ivicak99/universal-esp32-bridge/capinject.kicad_sch

## KiCad design capinject.kicad_sch (2026-05-29)

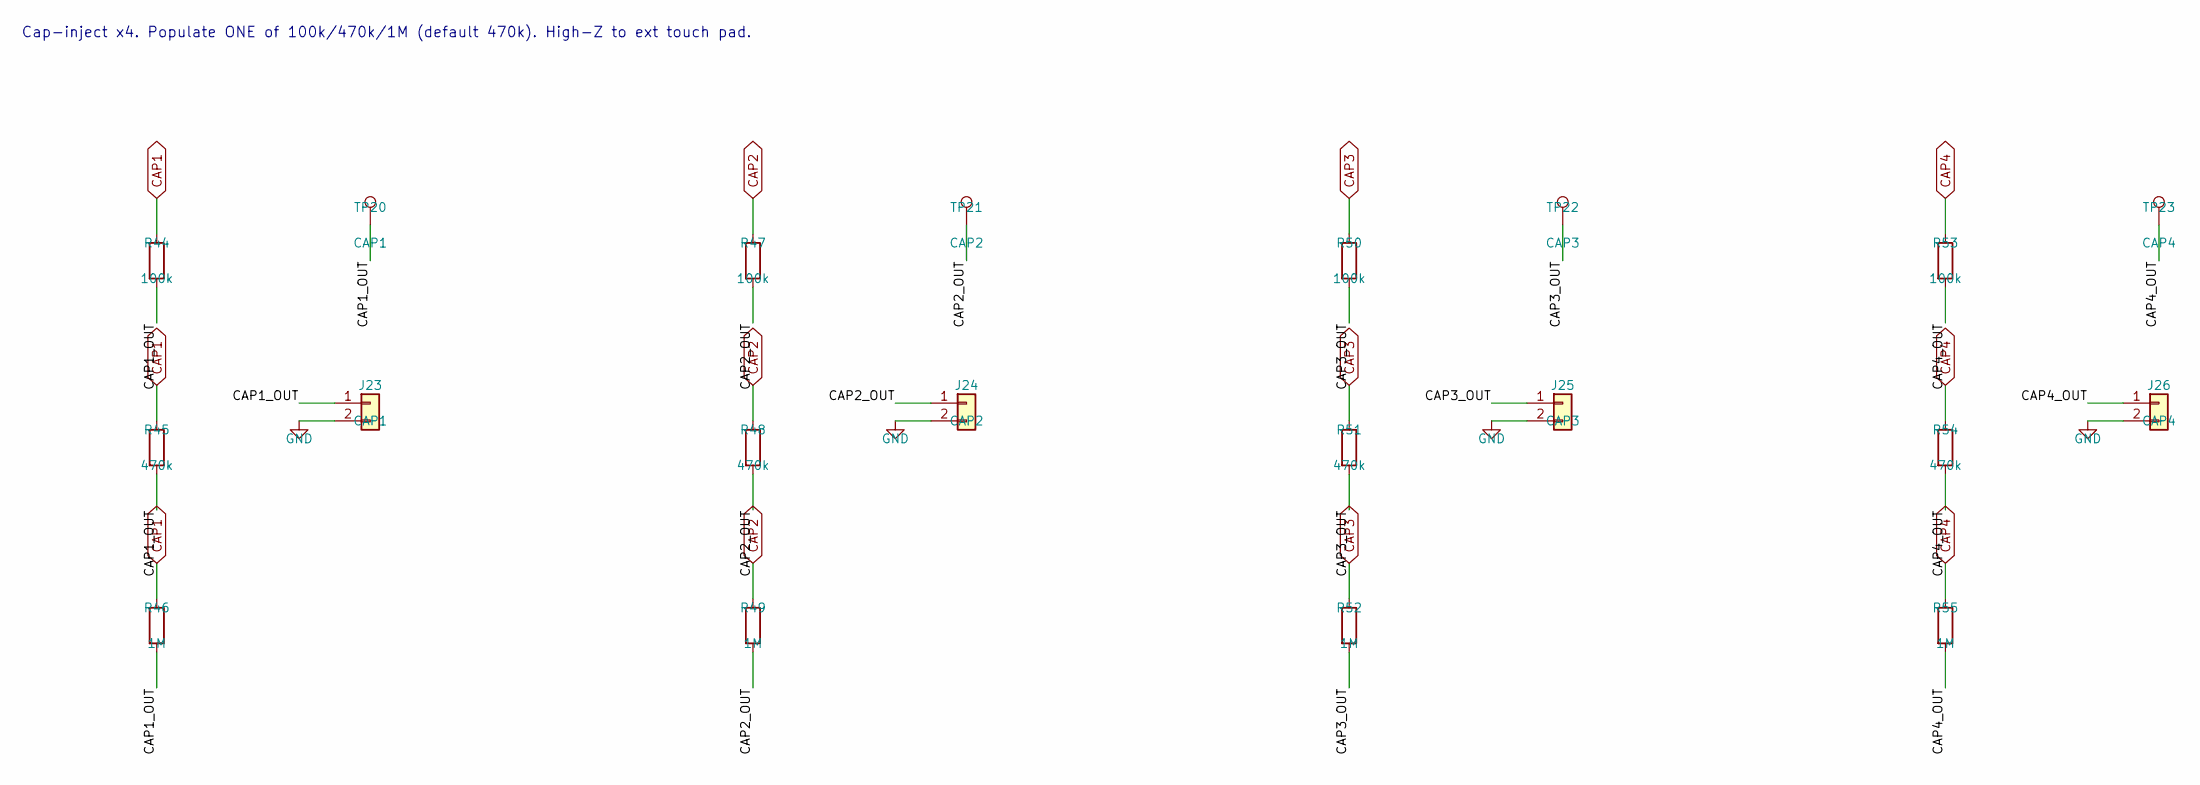
[picture p8: schematic capinject.kicad_sch]

Parts:
J23: CAP1; TerminalBlock_MaiXu_MX126-5.0-02P_1x02_P5.00mm
J24: CAP2; TerminalBlock_MaiXu_MX126-5.0-02P_1x02_P5.00mm
J25: CAP3; TerminalBlock_MaiXu_MX126-5.0-02P_1x02_P5.00mm
J26: CAP4; TerminalBlock_MaiXu_MX126-5.0-02P_1x02_P5.00mm
R44, R47, R50, R53: 100k; R_0603_1608Metric
R45, R48, R51, R54: 470k; R_0603_1608Metric
R46, R49, R52, R55: 1M; R_0603_1608Metric
TP20: CAP1; TestPoint_Pad_D1.5mm
TP21: CAP2; TestPoint_Pad_D1.5mm
TP22: CAP3; TestPoint_Pad_D1.5mm
TP23: CAP4; TestPoint_Pad_D1.5mm

Connections:
CAP1: R44.1, R45.1, R46.1
CAP1_OUT: J23.1, R44.2, R45.2, R46.2, TP20.1
CAP2: R47.1, R48.1, R49.1
CAP2_OUT: J24.1, R47.2, R48.2, R49.2, TP21.1
CAP3: R50.1, R51.1, R52.1
CAP3_OUT: J25.1, R50.2, R51.2, R52.2, TP22.1
CAP4: R53.1, R54.1, R55.1
CAP4_OUT: J26.1, R53.2, R54.2, R55.2, TP23.1
GND: J23.2, J24.2, J25.2, J26.2

Notes on the sheet:
Cap-inject x4. Populate ONE of 100k/470k/1M (default 470k). High-Z to ext touch pad.
