ivicak99/universal-esp32-bridge/inputs.kicad_sch

## KiCad design inputs.kicad_sch (2026-05-29)

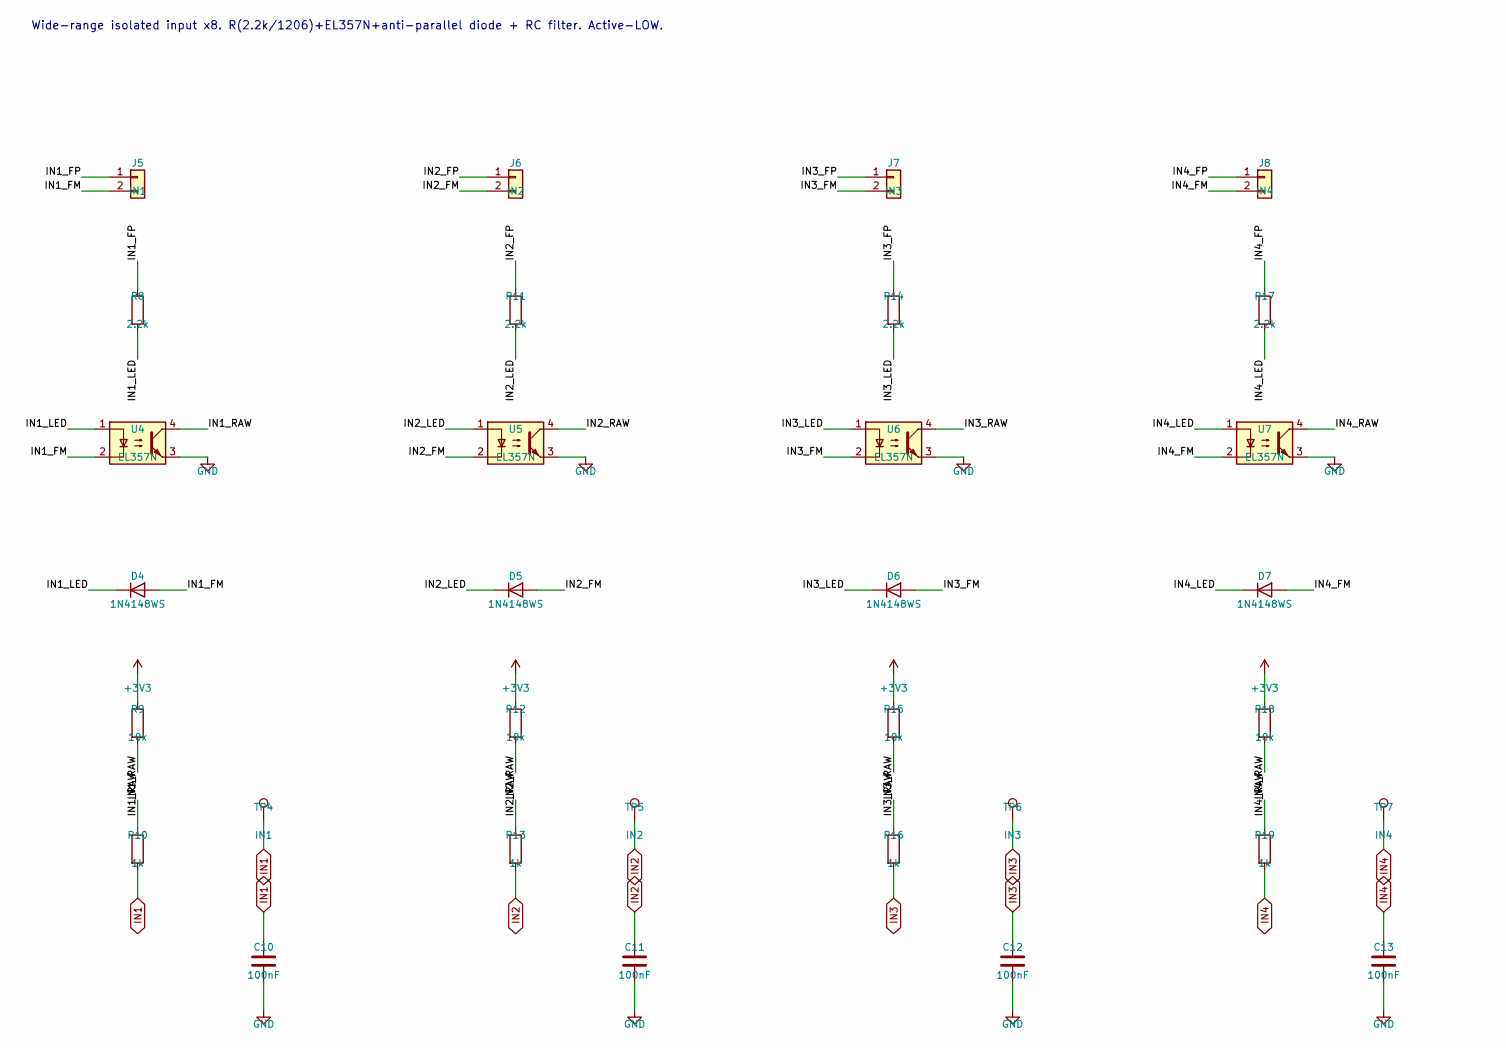
[picture p9: schematic inputs.kicad_sch, part in row 1, column 1]

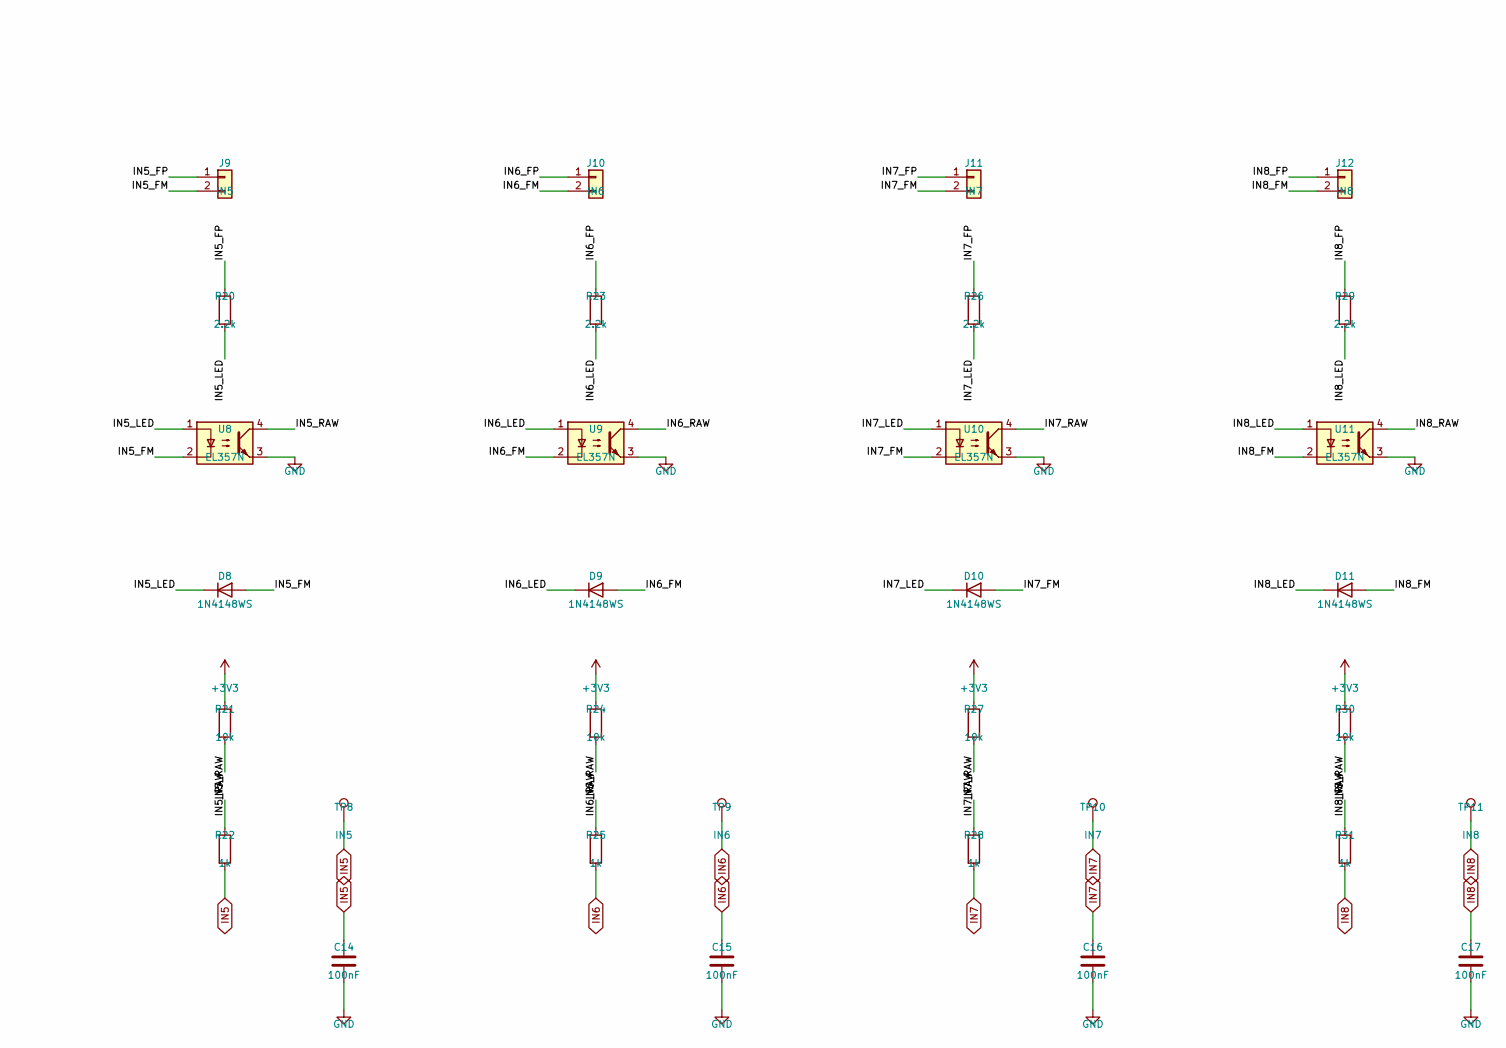
[picture p10: schematic inputs.kicad_sch, part in row 1, column 2]

Parts:
C10, C11, C12, C13, C14, C15, C16, C17: 100nF; C_0603_1608Metric
D4, D5, D6, D7, D8, D9, D10, D11: 1N4148WS; D_SOD-323
J5: IN1; TerminalBlock_MaiXu_MX126-5.0-02P_1x02_P5.00mm
J6: IN2; TerminalBlock_MaiXu_MX126-5.0-02P_1x02_P5.00mm
J7: IN3; TerminalBlock_MaiXu_MX126-5.0-02P_1x02_P5.00mm
J8: IN4; TerminalBlock_MaiXu_MX126-5.0-02P_1x02_P5.00mm
J9: IN5; TerminalBlock_MaiXu_MX126-5.0-02P_1x02_P5.00mm
J10: IN6; TerminalBlock_MaiXu_MX126-5.0-02P_1x02_P5.00mm
J11: IN7; TerminalBlock_MaiXu_MX126-5.0-02P_1x02_P5.00mm
J12: IN8; TerminalBlock_MaiXu_MX126-5.0-02P_1x02_P5.00mm
R8, R11, R14, R17, R20, R23, R26, R29: 2.2k; R_1206_3216Metric
R9, R12, R15, R18, R21, R24, R27, R30: 10k; R_0603_1608Metric
R10, R13, R16, R19, R22, R25, R28, R31: 1k; R_0603_1608Metric
TP4: IN1; TestPoint_Pad_D1.5mm
TP5: IN2; TestPoint_Pad_D1.5mm
TP6: IN3; TestPoint_Pad_D1.5mm
TP7: IN4; TestPoint_Pad_D1.5mm
TP8: IN5; TestPoint_Pad_D1.5mm
TP9: IN6; TestPoint_Pad_D1.5mm
TP10: IN7; TestPoint_Pad_D1.5mm
TP11: IN8; TestPoint_Pad_D1.5mm
U4, U5, U6, U7, U8, U9, U10, U11: EL357N; EL357N_SOP-4

Connections:
+3V3: R9.1, R12.1, R15.1, R18.1, R21.1, R24.1, R27.1, R30.1
GND: C10.2, C11.2, C12.2, C13.2, C14.2, C15.2, C16.2, C17.2, U4.3, U5.3, U6.3, U7.3, U8.3, U9.3, U10.3, U11.3
IN1: C10.1, R10.2, TP4.1
IN1_FM: D4.2 (A), J5.2, U4.2
IN1_FP: J5.1, R8.1
IN1_LED: D4.1 (K), R8.2, U4.1
IN1_RAW: R9.2, R10.1, U4.4
IN2: C11.1, R13.2, TP5.1
IN2_FM: D5.2 (A), J6.2, U5.2
IN2_FP: J6.1, R11.1
IN2_LED: D5.1 (K), R11.2, U5.1
IN2_RAW: R12.2, R13.1, U5.4
IN3: C12.1, R16.2, TP6.1
IN3_FM: D6.2 (A), J7.2, U6.2
IN3_FP: J7.1, R14.1
IN3_LED: D6.1 (K), R14.2, U6.1
IN3_RAW: R15.2, R16.1, U6.4
IN4: C13.1, R19.2, TP7.1
IN4_FM: D7.2 (A), J8.2, U7.2
IN4_FP: J8.1, R17.1
IN4_LED: D7.1 (K), R17.2, U7.1
IN4_RAW: R18.2, R19.1, U7.4
IN5: C14.1, R22.2, TP8.1
IN5_FM: D8.2 (A), J9.2, U8.2
IN5_FP: J9.1, R20.1
IN5_LED: D8.1 (K), R20.2, U8.1
IN5_RAW: R21.2, R22.1, U8.4
IN6: C15.1, R25.2, TP9.1
IN6_FM: D9.2 (A), J10.2, U9.2
IN6_FP: J10.1, R23.1
IN6_LED: D9.1 (K), R23.2, U9.1
IN6_RAW: R24.2, R25.1, U9.4
IN7: C16.1, R28.2, TP10.1
IN7_FM: D10.2 (A), J11.2, U10.2
IN7_FP: J11.1, R26.1
IN7_LED: D10.1 (K), R26.2, U10.1
IN7_RAW: R27.2, R28.1, U10.4
IN8: C17.1, R31.2, TP11.1
IN8_FM: D11.2 (A), J12.2, U11.2
IN8_FP: J12.1, R29.1
IN8_LED: D11.1 (K), R29.2, U11.1
IN8_RAW: R30.2, R31.1, U11.4

Notes on the sheet:
Wide-range isolated input x8. R(2.2k/1206)+EL357N+anti-parallel diode + RC filter. Active-LOW.
