ivicak99/universal-esp32-bridge/mcu.kicad_sch

## KiCad design mcu.kicad_sch (2026-05-29)

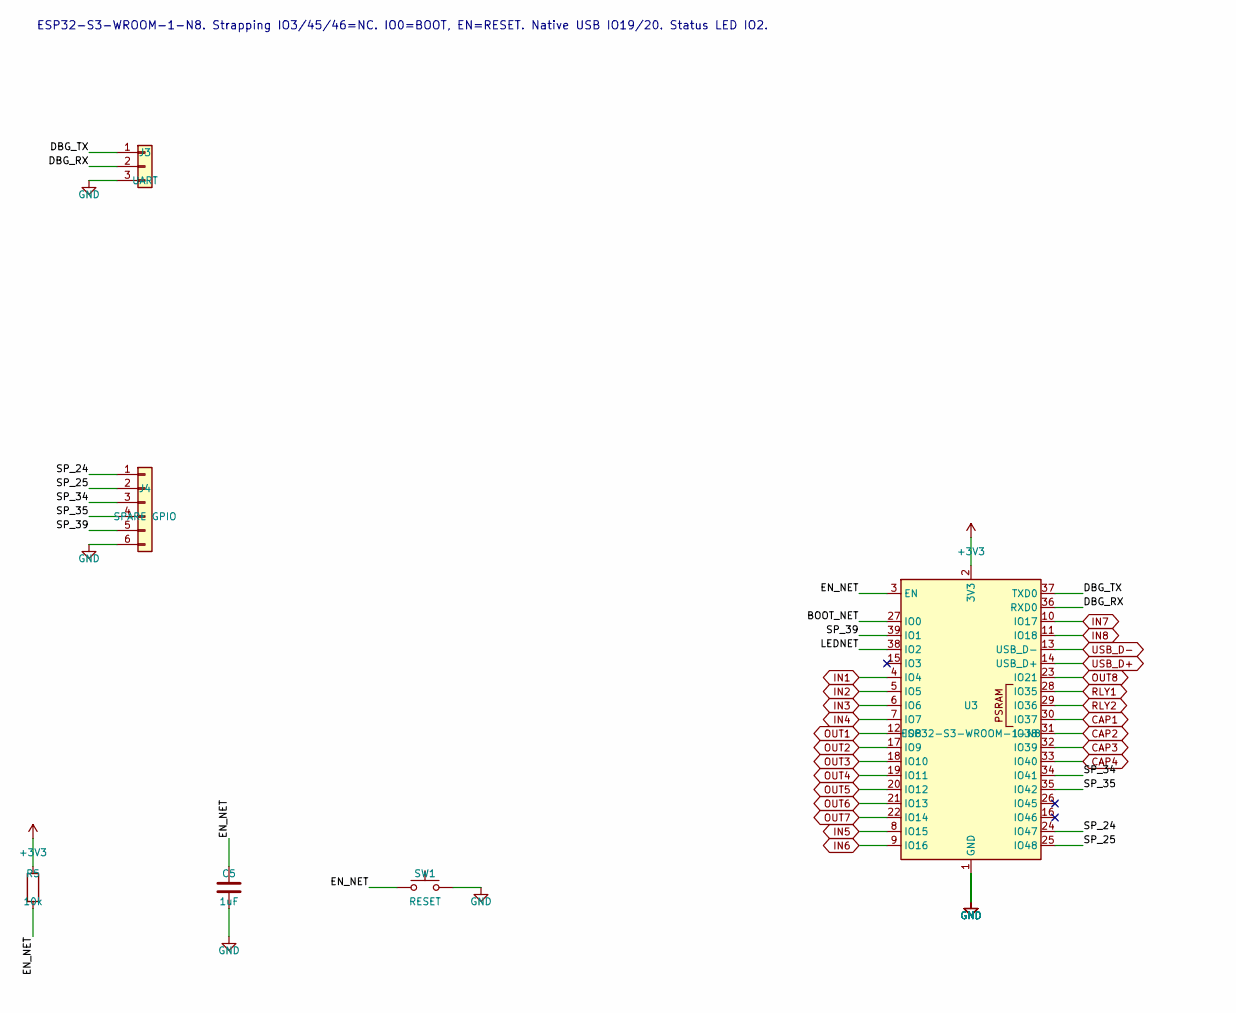
[picture p11: schematic mcu.kicad_sch, part in row 1, column 1]

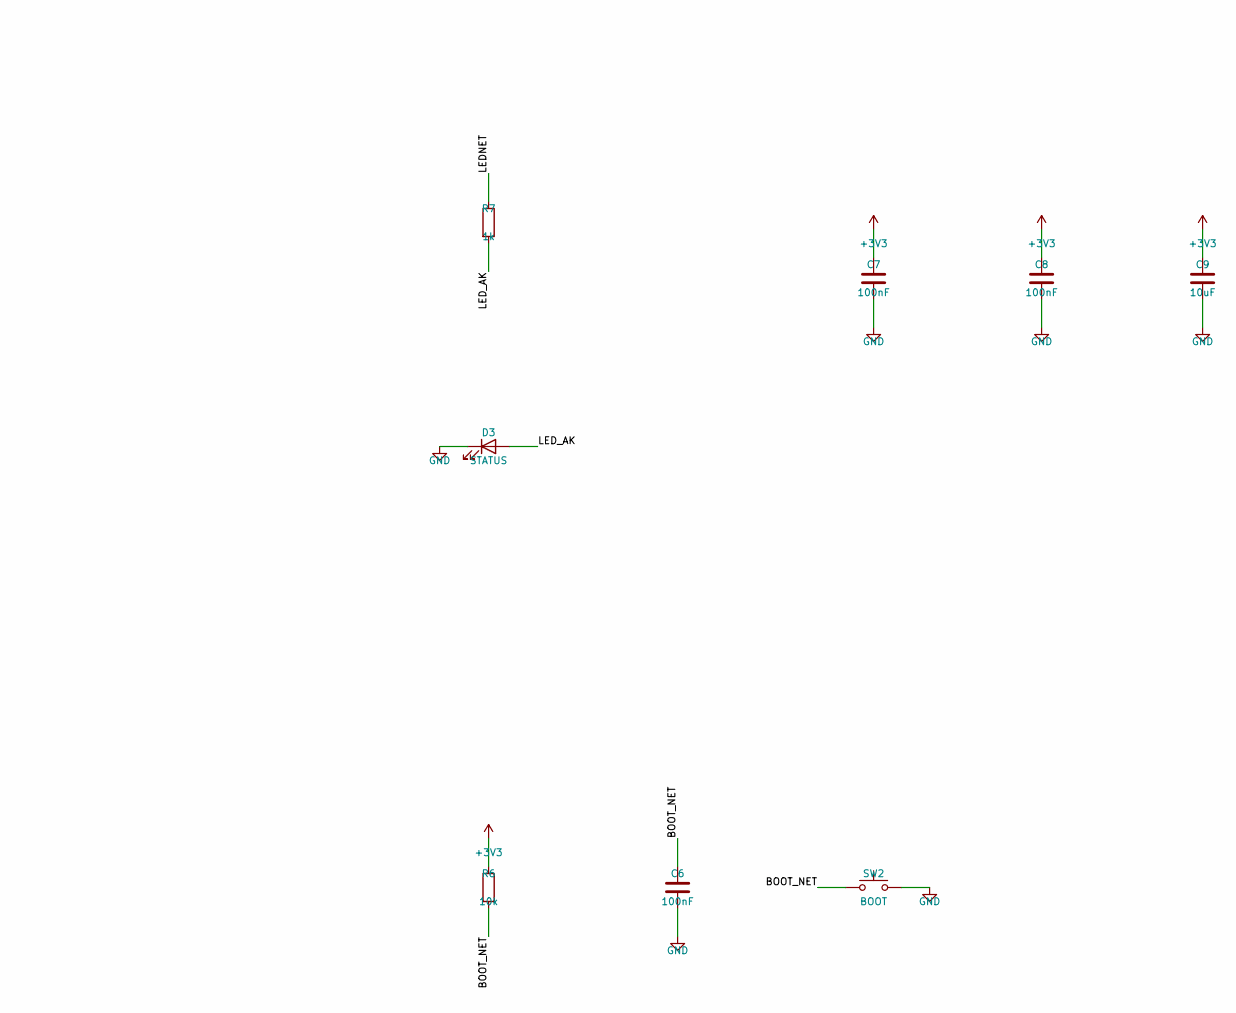
[picture p12: schematic mcu.kicad_sch, part in row 1, column 2]

Parts:
C5: 1uF; C_0603_1608Metric
C6, C7, C8: 100nF; C_0603_1608Metric
C9: 10uF; C_0603_1608Metric
D3: STATUS; LED_0603_1608Metric
J3: UART; PinHeader_1x03_P2.54mm_Vertical
J4: SPARE GPIO; PinHeader_1x06_P2.54mm_Vertical
R5, R6: 10k; R_0603_1608Metric
R7: 1k; R_0603_1608Metric
SW1: RESET; Panasonic_EVQPUJ_EVQPUA
SW2: BOOT; Panasonic_EVQPUJ_EVQPUA
U3: ESP32-S3-WROOM-1-N8; ESP32-S3-WROOM-1

Connections:
+3V3: C7.1, C8.1, C9.1, R5.1, R6.1, U3.2 (3V3)
BOOT_NET: C6.1, R6.2, SW2.1, U3.27 (IO0)
CAP1: U3.30 (IO37)
CAP2: U3.31 (IO38)
CAP3: U3.32 (IO39)
CAP4: U3.33 (IO40)
DBG_RX: J3.2, U3.36 (RXD0)
DBG_TX: J3.1, U3.37 (TXD0)
EN_NET: C5.1, R5.2, SW1.1, U3.3 (EN)
GND: C5.2, C6.2, C7.2, C8.2, C9.2, D3.1 (K), J3.3, J4.6, SW1.2, SW2.2, U3.1 (GND), U3.40 (GND), U3.41 (GND)
IN1: U3.4 (IO4)
IN2: U3.5 (IO5)
IN3: U3.6 (IO6)
IN4: U3.7 (IO7)
IN5: U3.8 (IO15)
IN6: U3.9 (IO16)
IN7: U3.10 (IO17)
IN8: U3.11 (IO18)
LEDNET: R7.1, U3.38 (IO2)
LED_AK: D3.2 (A), R7.2
OUT1: U3.12 (IO8)
OUT2: U3.17 (IO9)
OUT3: U3.18 (IO10)
OUT4: U3.19 (IO11)
OUT5: U3.20 (IO12)
OUT6: U3.21 (IO13)
OUT7: U3.22 (IO14)
OUT8: U3.23 (IO21)
RLY1: U3.28 (IO35)
RLY2: U3.29 (IO36)
SP_24: J4.1, U3.24 (IO47)
SP_25: J4.2, U3.25 (IO48)
SP_34: J4.3, U3.34 (IO41)
SP_35: J4.4, U3.35 (IO42)
SP_39: J4.5, U3.39 (IO1)
USB_D+: U3.14 (USB_D+)
USB_D-: U3.13 (USB_D-)

Notes on the sheet:
ESP32-S3-WROOM-1-N8. Strapping IO3/45/46=NC. IO0=BOOT, EN=RESET. Native USB IO19/20. Status LED IO2.
