ivicak99/universal-esp32-bridge/photomos.kicad_sch

## KiCad design photomos.kicad_sch (2026-05-29)

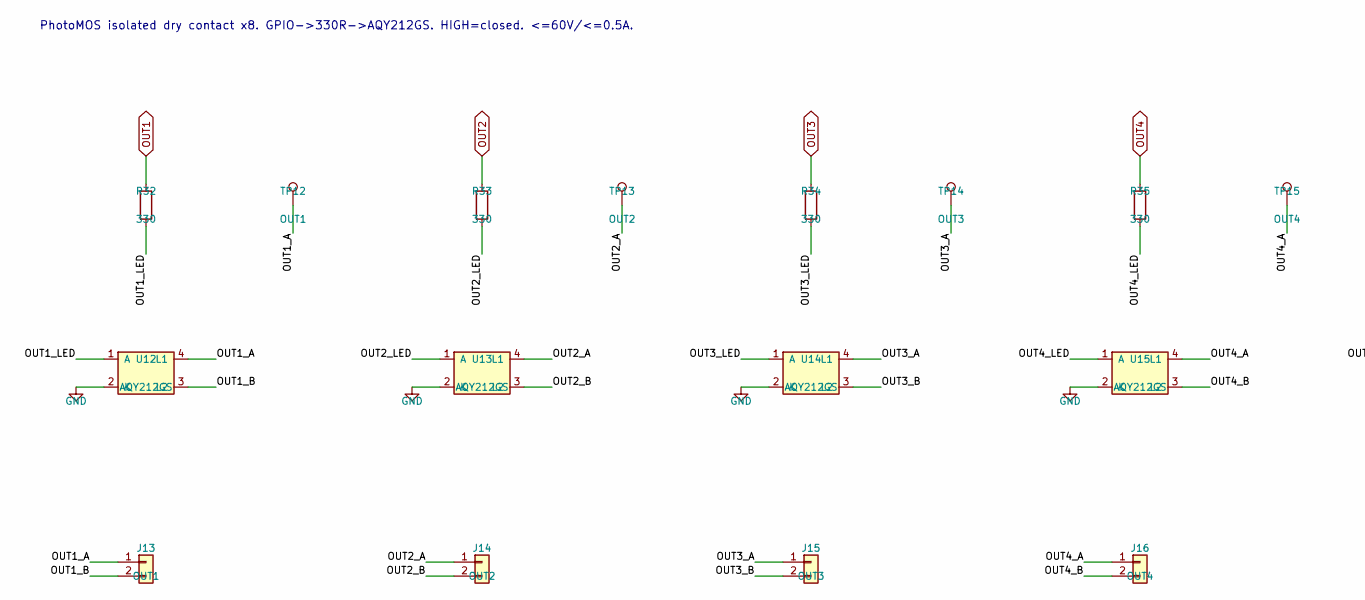
[picture p13: schematic photomos.kicad_sch, part in row 1, column 1]

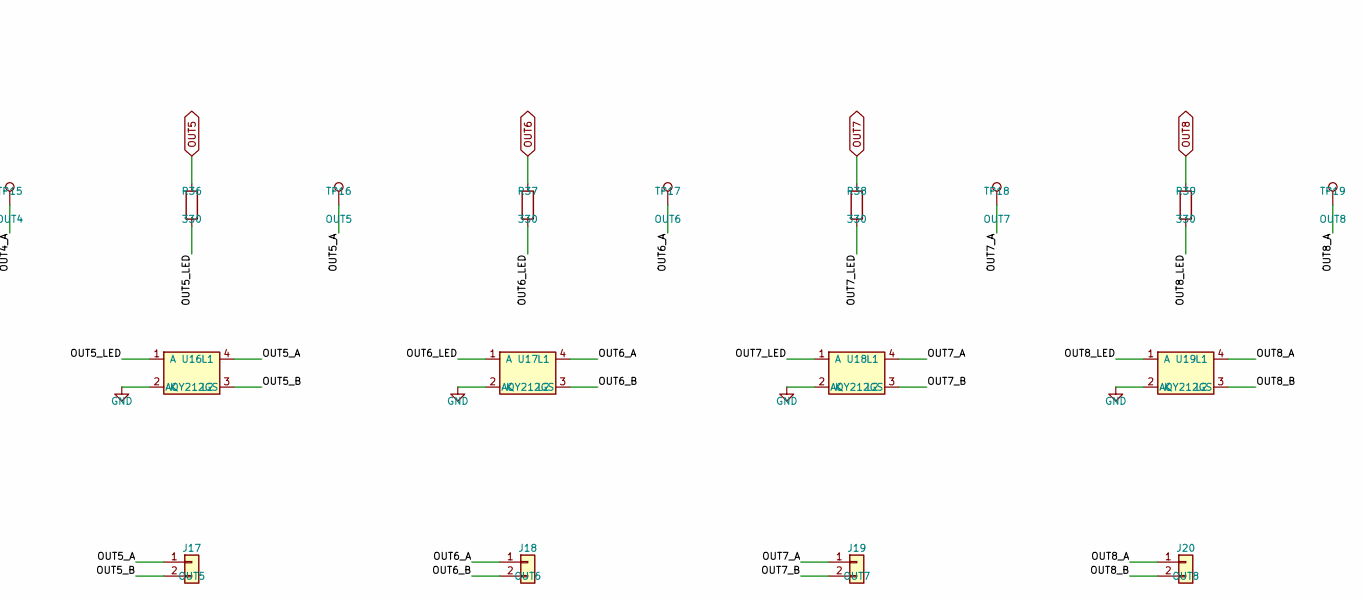
[picture p14: schematic photomos.kicad_sch, part in row 1, column 2]

Parts:
J13: OUT1; TerminalBlock_MaiXu_MX126-5.0-02P_1x02_P5.00mm
J14: OUT2; TerminalBlock_MaiXu_MX126-5.0-02P_1x02_P5.00mm
J15: OUT3; TerminalBlock_MaiXu_MX126-5.0-02P_1x02_P5.00mm
J16: OUT4; TerminalBlock_MaiXu_MX126-5.0-02P_1x02_P5.00mm
J17: OUT5; TerminalBlock_MaiXu_MX126-5.0-02P_1x02_P5.00mm
J18: OUT6; TerminalBlock_MaiXu_MX126-5.0-02P_1x02_P5.00mm
J19: OUT7; TerminalBlock_MaiXu_MX126-5.0-02P_1x02_P5.00mm
J20: OUT8; TerminalBlock_MaiXu_MX126-5.0-02P_1x02_P5.00mm
R32, R33, R34, R35, R36, R37, R38, R39: 330; R_0603_1608Metric
TP12: OUT1; TestPoint_Pad_D1.5mm
TP13: OUT2; TestPoint_Pad_D1.5mm
TP14: OUT3; TestPoint_Pad_D1.5mm
TP15: OUT4; TestPoint_Pad_D1.5mm
TP16: OUT5; TestPoint_Pad_D1.5mm
TP17: OUT6; TestPoint_Pad_D1.5mm
TP18: OUT7; TestPoint_Pad_D1.5mm
TP19: OUT8; TestPoint_Pad_D1.5mm
U12, U13, U14, U15, U16, U17, U18, U19: AQY212GS; AQY212GS_SOP-4

Connections:
GND: U12.2 (K), U13.2 (K), U14.2 (K), U15.2 (K), U16.2 (K), U17.2 (K), U18.2 (K), U19.2 (K)
OUT1: R32.1
OUT1_A: J13.1, TP12.1, U12.4 (L1)
OUT1_B: J13.2, U12.3 (L2)
OUT1_LED: R32.2, U12.1 (A)
OUT2: R33.1
OUT2_A: J14.1, TP13.1, U13.4 (L1)
OUT2_B: J14.2, U13.3 (L2)
OUT2_LED: R33.2, U13.1 (A)
OUT3: R34.1
OUT3_A: J15.1, TP14.1, U14.4 (L1)
OUT3_B: J15.2, U14.3 (L2)
OUT3_LED: R34.2, U14.1 (A)
OUT4: R35.1
OUT4_A: J16.1, TP15.1, U15.4 (L1)
OUT4_B: J16.2, U15.3 (L2)
OUT4_LED: R35.2, U15.1 (A)
OUT5: R36.1
OUT5_A: J17.1, TP16.1, U16.4 (L1)
OUT5_B: J17.2, U16.3 (L2)
OUT5_LED: R36.2, U16.1 (A)
OUT6: R37.1
OUT6_A: J18.1, TP17.1, U17.4 (L1)
OUT6_B: J18.2, U17.3 (L2)
OUT6_LED: R37.2, U17.1 (A)
OUT7: R38.1
OUT7_A: J19.1, TP18.1, U18.4 (L1)
OUT7_B: J19.2, U18.3 (L2)
OUT7_LED: R38.2, U18.1 (A)
OUT8: R39.1
OUT8_A: J20.1, TP19.1, U19.4 (L1)
OUT8_B: J20.2, U19.3 (L2)
OUT8_LED: R39.2, U19.1 (A)

Notes on the sheet:
PhotoMOS isolated dry contact x8. GPIO->330R->AQY212GS. HIGH=closed. <=60V/<=0.5A.
