ivicak99/universal-esp32-bridge/power.kicad_sch

## KiCad design power.kicad_sch (2026-05-29)

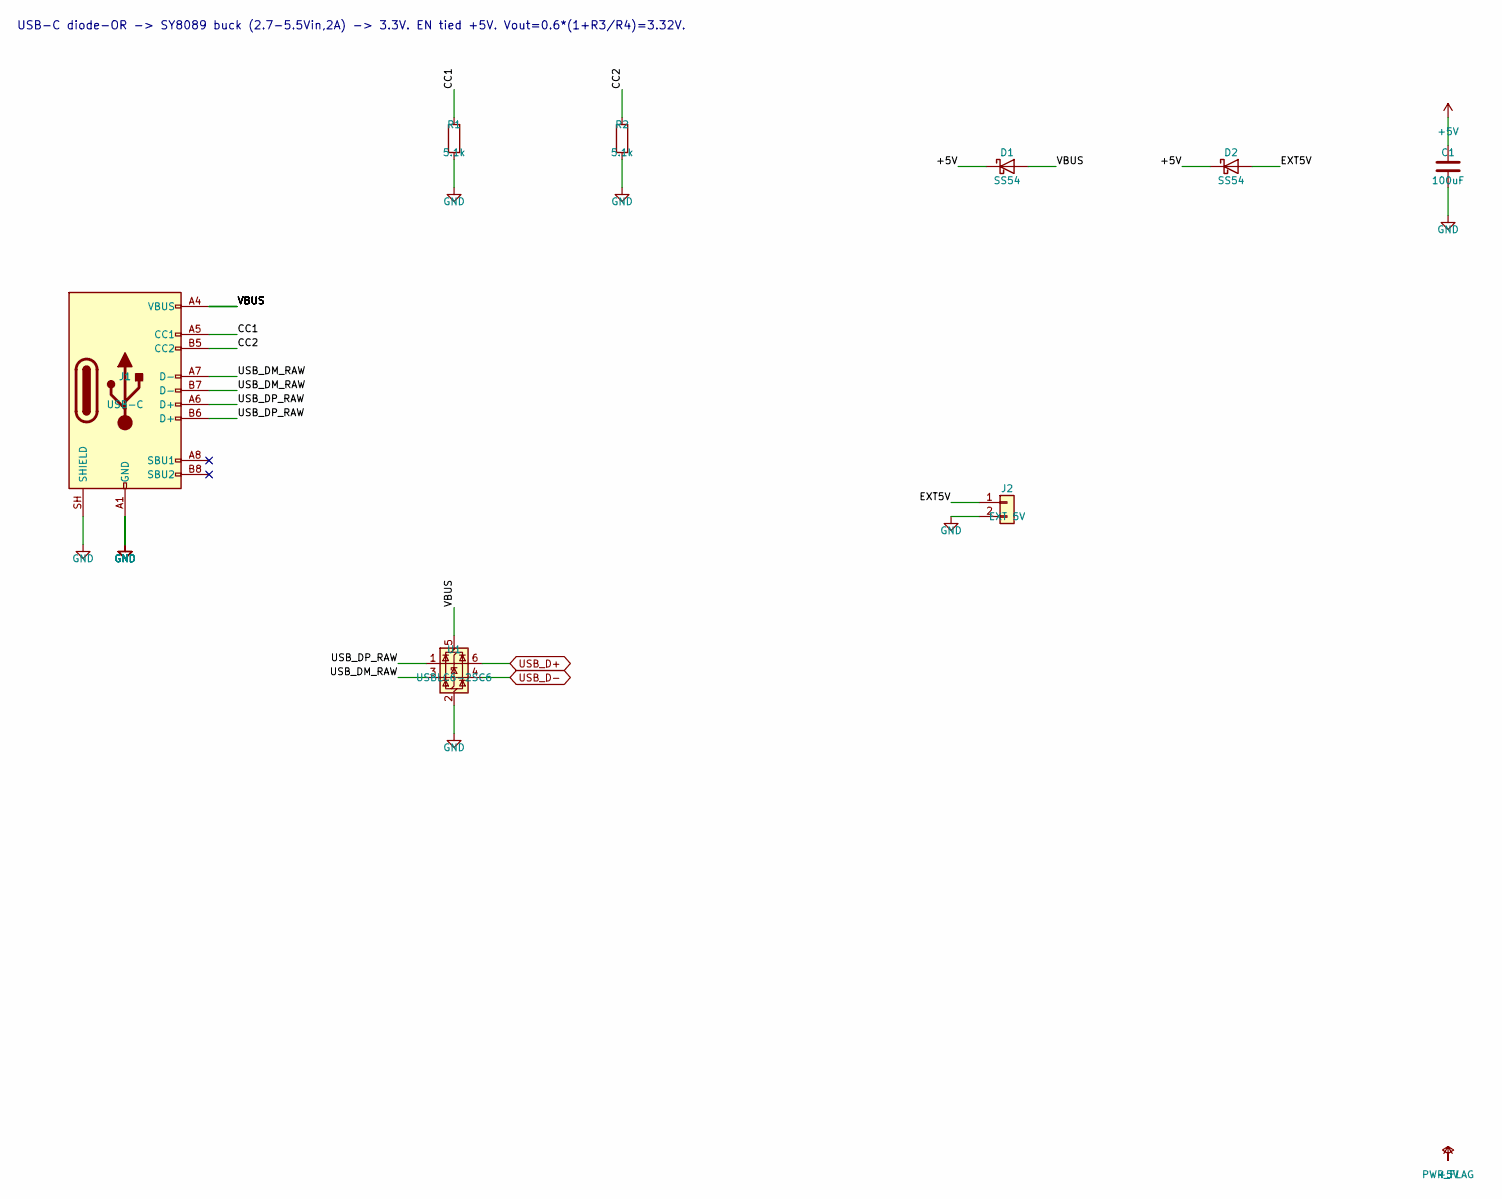
[picture p15: schematic power.kicad_sch, part in row 1, column 1]

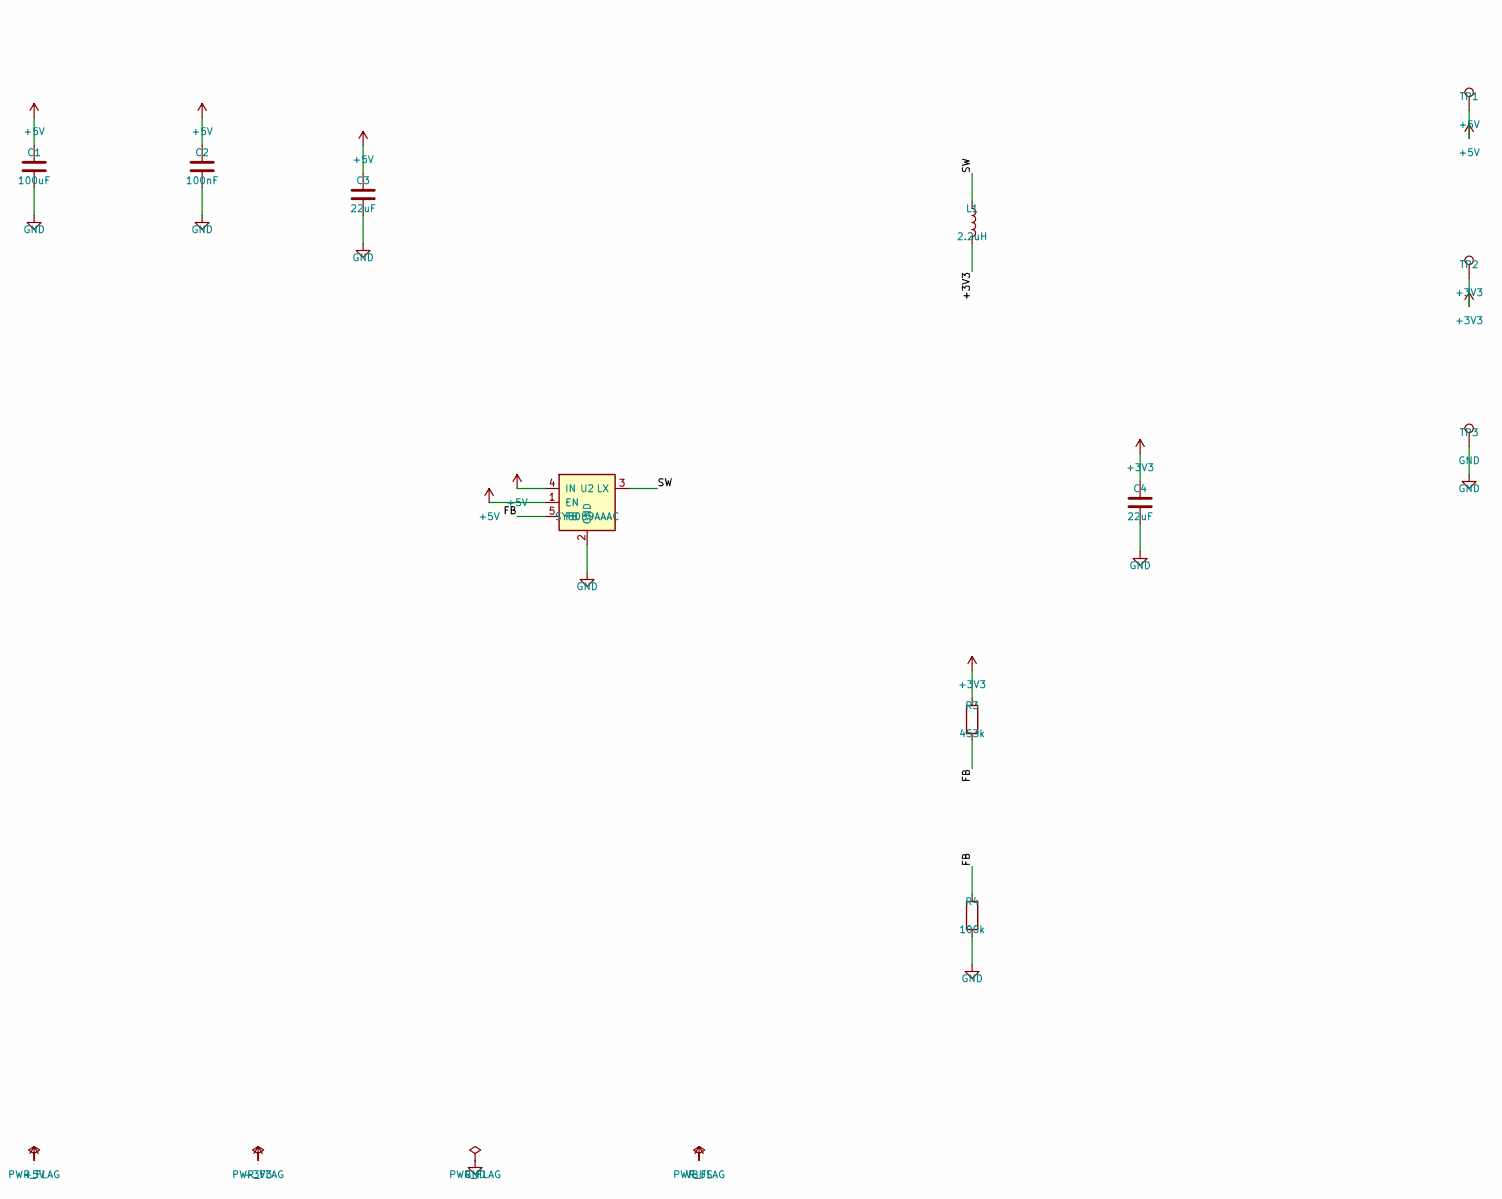
[picture p16: schematic power.kicad_sch, part in row 1, column 2]

Parts:
C1: 100uF; C_1206_3216Metric
C2: 100nF; C_0603_1608Metric
C3, C4: 22uF; C_0805_2012Metric
D1, D2: SS54; D_SMC
J1: USB-C; USB_C_Receptacle_HRO_TYPE-C-31-M-12
J2: EXT 5V; TerminalBlock_MaiXu_MX126-5.0-02P_1x02_P5.00mm
L1: 2.2uH; L_1210_3225Metric
R1, R2: 5.1k; R_0603_1608Metric
R3: 453k; R_0603_1608Metric
R4: 100k; R_0603_1608Metric
TP1: +5V; TestPoint_Pad_D1.5mm
TP2: +3V3; TestPoint_Pad_D1.5mm
TP3: GND; TestPoint_Pad_D1.5mm
U1: USBLC6-2SC6; SOT-23-6
U2: SY8089AAAC; SOT-23-5

Connections:
+3V3: C1.1, C1.2, C2.1, C2.2, C3.1, C3.2, C4.1, C4.2, J1.A1 (GND), J1.A12 (GND), J1.B1 (GND), J1.B12 (GND), J1.SH (SHIELD), J2.2, L1.2, R1.2, R2.2, R3.1, R4.2, TP1.1, TP2.1, TP3.1, U1.2 (GND), U2.1 (EN), U2.2 (GND), U2.4 (IN)
+5V: D1.1 (K), D2.1 (K)
CC1: J1.A5 (CC1), R1.1
CC2: J1.B5 (CC2), R2.1
EXT5V: D2.2 (A), J2.1
FB: R3.2, R4.1, U2.5 (FB)
SW: L1.1, U2.3 (LX)
USB_D+: U1.6 (I/O1)
USB_D-: U1.4 (I/O2)
USB_DM_RAW: J1.A7 (D-), J1.B7 (D-), U1.3 (I/O2)
USB_DP_RAW: J1.A6 (D+), J1.B6 (D+), U1.1 (I/O1)
VBUS: D1.2 (A), J1.A4 (VBUS), J1.A9 (VBUS), J1.B4 (VBUS), J1.B9 (VBUS), U1.5 (VBUS)

Notes on the sheet:
USB-C diode-OR -> SY8089 buck (2.7-5.5Vin,2A) -> 3.3V. EN tied +5V. Vout=0.6*(1+R3/R4)=3.32V.
