ivicak99/universal-esp32-bridge/relays.kicad_sch

## KiCad design relays.kicad_sch (2026-05-29)

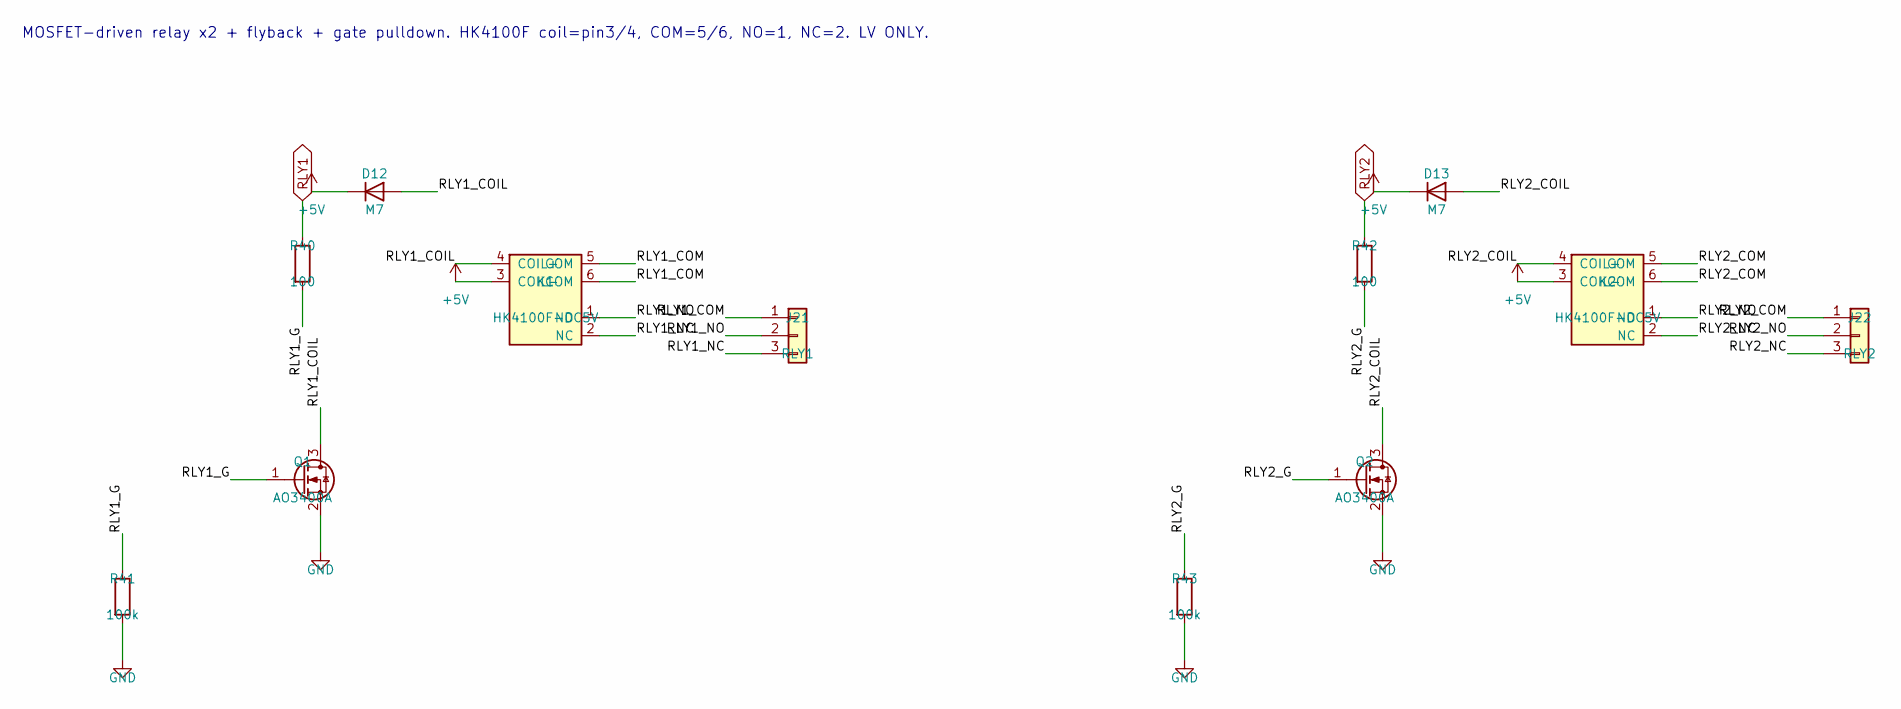
[picture p17: schematic relays.kicad_sch]

Parts:
D12, D13: M7; D_SMA
J21: RLY1; TerminalBlock_MaiXu_MX126-5.0-03P_1x03_P5.00mm
J22: RLY2; TerminalBlock_MaiXu_MX126-5.0-03P_1x03_P5.00mm
K1, K2: HK4100F-DC5V; HK4100F-DC5V-SHG
Q1, Q2: AO3400A; SOT-23
R40, R42: 100; R_0603_1608Metric
R41, R43: 100k; R_0603_1608Metric

Connections:
+5V: D12.1 (K), D13.1 (K), K1.3 (COIL-), K2.3 (COIL-)
GND: Q1.2 (S), Q2.2 (S), R41.2, R43.2
RLY1: R40.1
RLY1_COIL: D12.2 (A), K1.4 (COIL+), Q1.3 (D)
RLY1_COM: J21.1, K1.5 (COM), K1.6 (COM)
RLY1_G: Q1.1 (G), R40.2, R41.1
RLY1_NC: J21.3, K1.2 (NC)
RLY1_NO: J21.2, K1.1 (NO)
RLY2: R42.1
RLY2_COIL: D13.2 (A), K2.4 (COIL+), Q2.3 (D)
RLY2_COM: J22.1, K2.5 (COM), K2.6 (COM)
RLY2_G: Q2.1 (G), R42.2, R43.1
RLY2_NC: J22.3, K2.2 (NC)
RLY2_NO: J22.2, K2.1 (NO)

Notes on the sheet:
MOSFET-driven relay x2 + flyback + gate pulldown. HK4100F coil=pin3/4, COM=5/6, NO=1, NC=2. LV ONLY.
